nathancharlesjones/STM32F103C8T6-breakout-board_compact/Pictures/P3080385.JPG

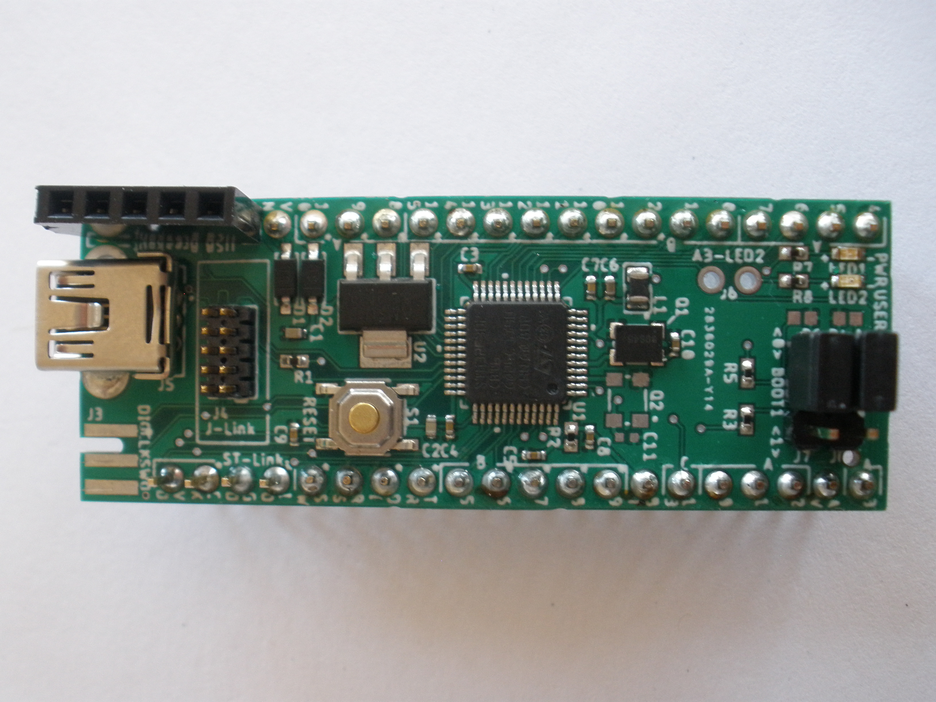
Pictures/P3080385.JPG
